kisonecat/corne-case/top.scad

include <case.scad>
the_top();
